jvyduna/BCWW-sign-2018/Physical sign design/CAD/1 HOT/Cuts/Front panel/0.25 layer cuts.pdf

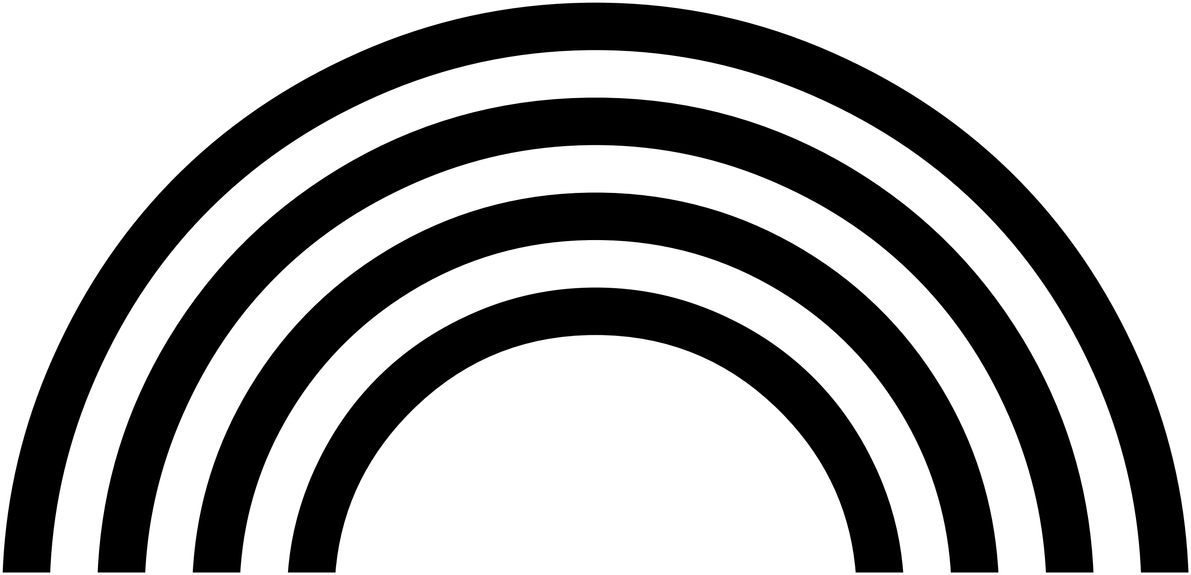
[picture p3: figure]
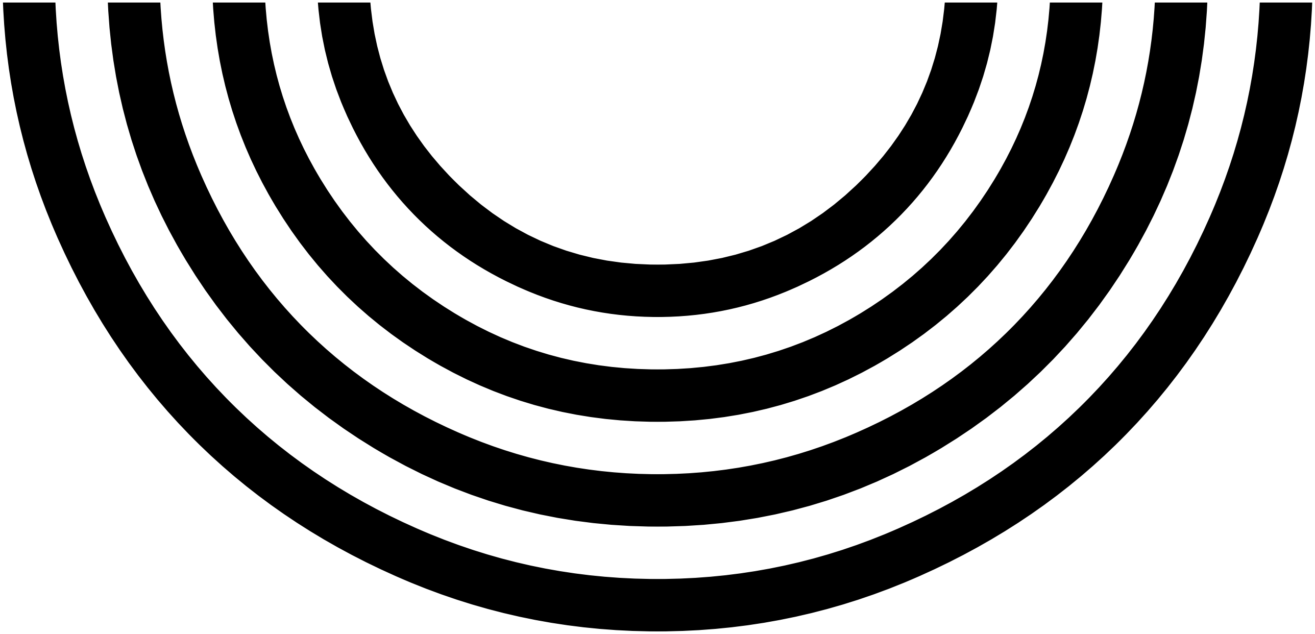
[picture p4: figure]
