jvyduna/BCWW-sign-2018/Physical sign design/CAD/3 CHICKA/Cuts/Border channel/cut path border.pdf

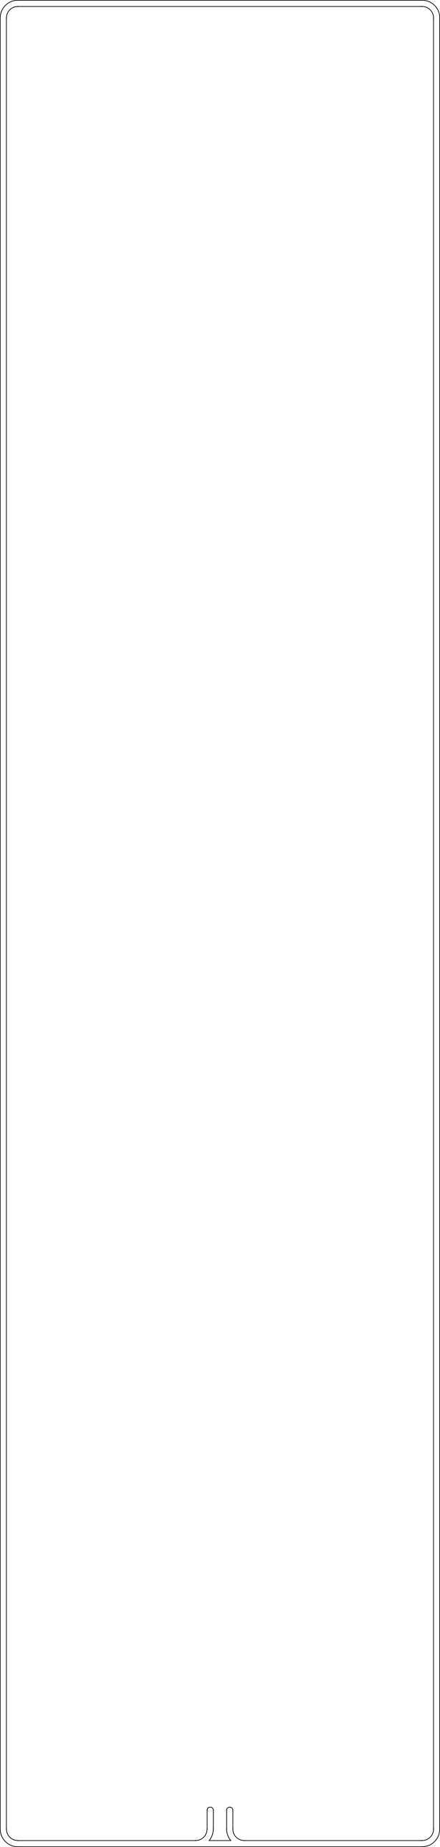
[picture p5: figure]
