jvyduna/BCWW-sign-2018/Physical sign design/2018 Camp placement.png

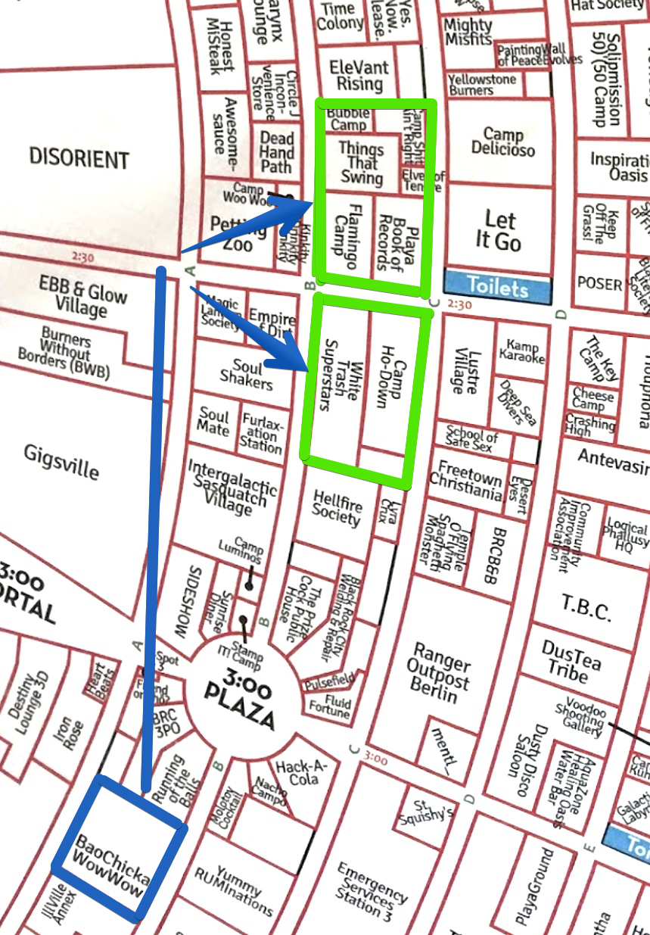
Physical sign design/2018 Camp placement.png
