jvyduna/BCWW-sign-2018/Physical sign design/BCWW signs sunset.jpg

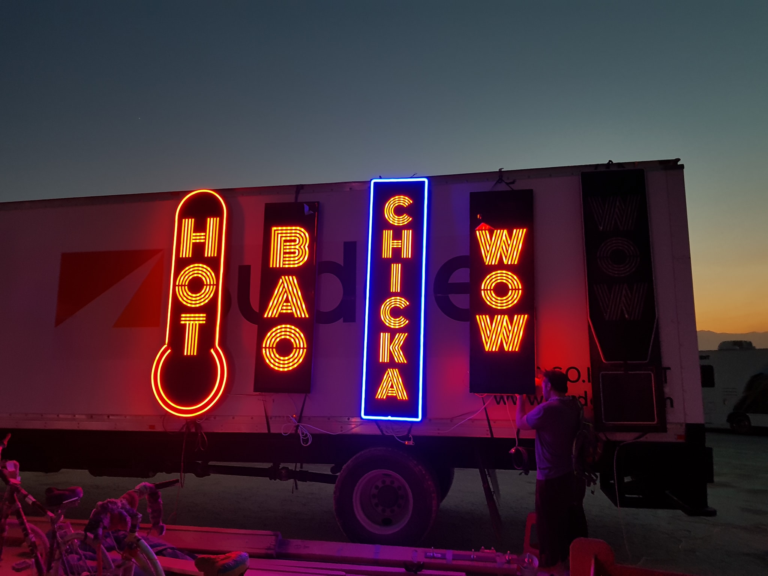
Physical sign design/BCWW signs sunset.jpg
