jvyduna/BCWW-sign-2018/Physical sign design/fonts/mockups/Bauhaus.png

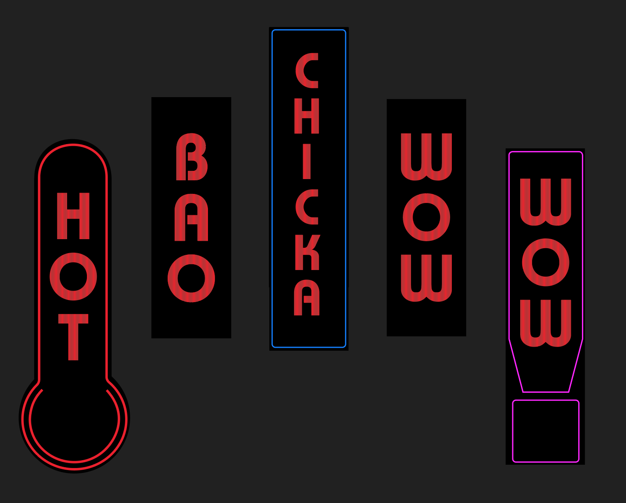
Physical sign design/fonts/mockups/Bauhaus.png
