jvyduna/BCWW-sign-2018/Physical sign design/fonts/mockups/Bungee.png

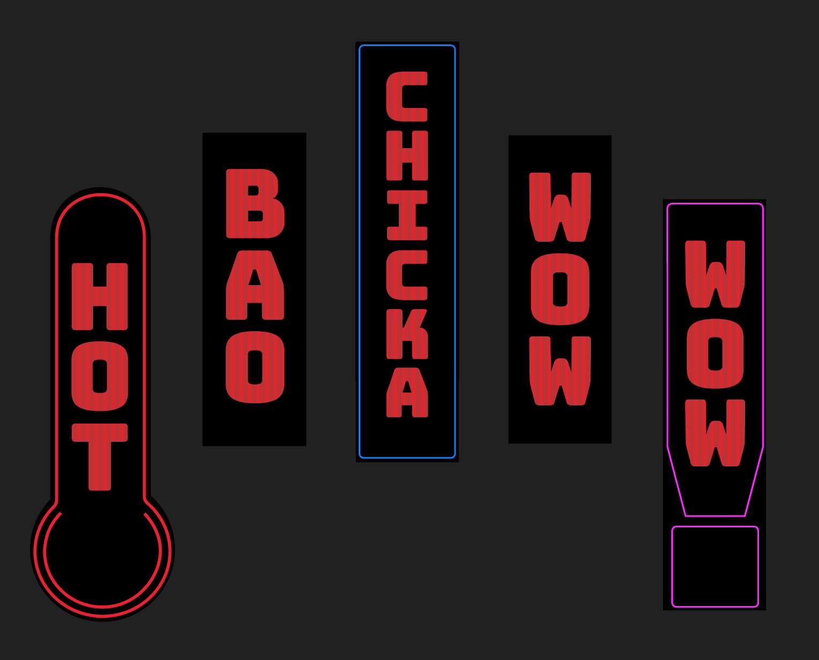
Physical sign design/fonts/mockups/Bungee.png
