jvyduna/BCWW-sign-2018/Physical sign design/fonts/mockups/Delicious.png

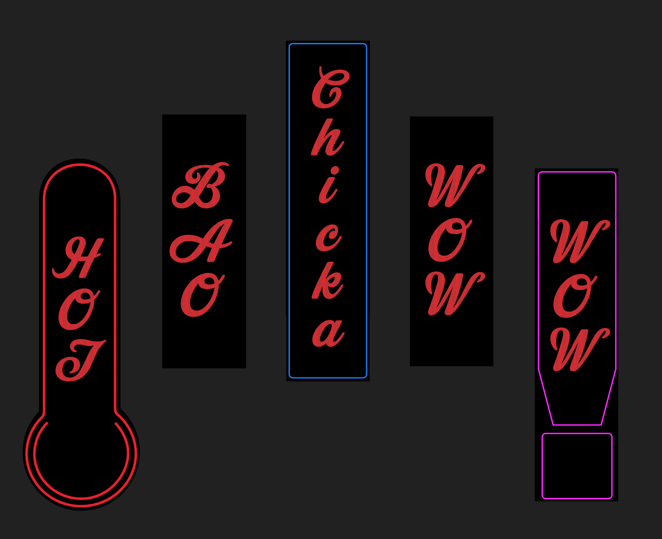
Physical sign design/fonts/mockups/Delicious.png
