jvyduna/BCWW-sign-2018/Physical sign design/fonts/mockups/Idlewild Bold.png

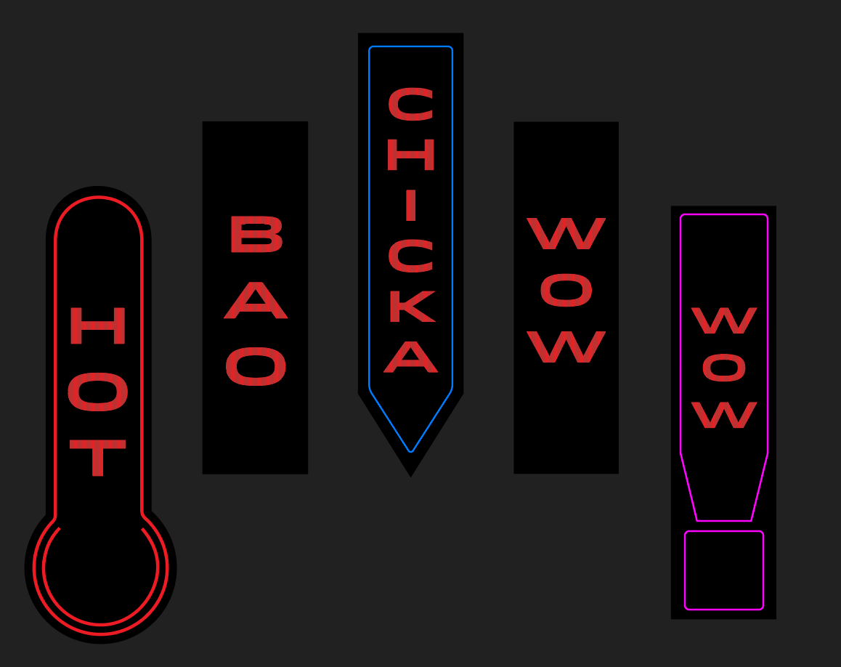
Physical sign design/fonts/mockups/Idlewild Bold.png
