jvyduna/BCWW-sign-2018/Physical sign design/fonts/mockups/Monoton.png

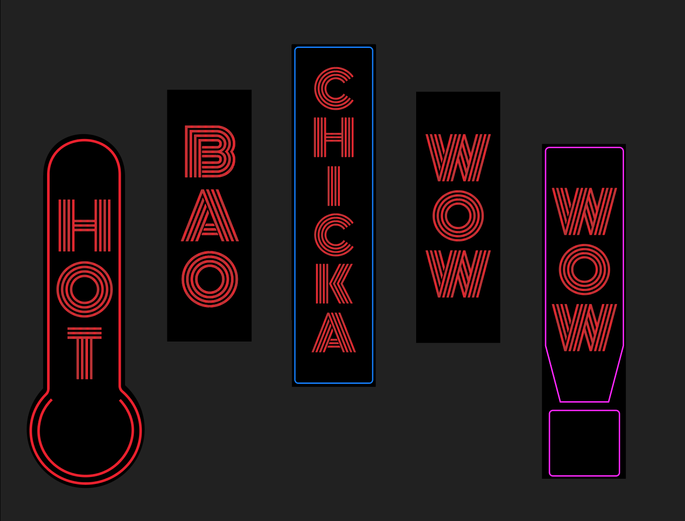
Physical sign design/fonts/mockups/Monoton.png
