jvyduna/BCWW-sign-2018/Physical sign design/fonts/mockups/Ringside.png

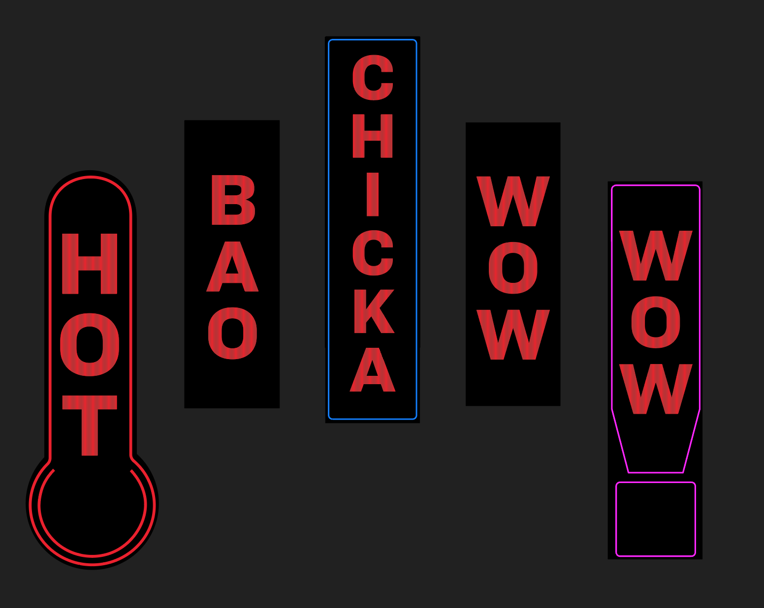
Physical sign design/fonts/mockups/Ringside.png
