jvyduna/BCWW-sign-2018/Physical sign design/Inspiration board/40342030-neon-light-alphabet-font-.jpg

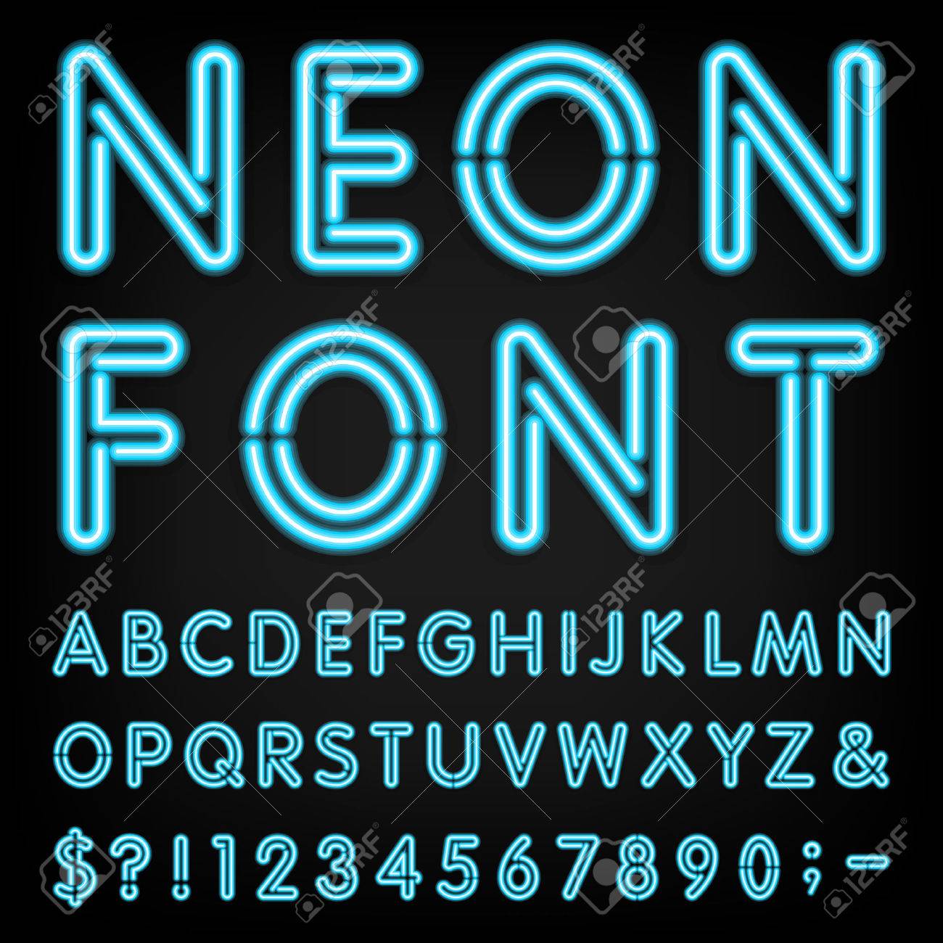
Physical sign design/Inspiration board/40342030-neon-light-alphabet-font-.jpg
