jvyduna/BCWW-sign-2018/Physical sign design/Inspiration board/img.jpg

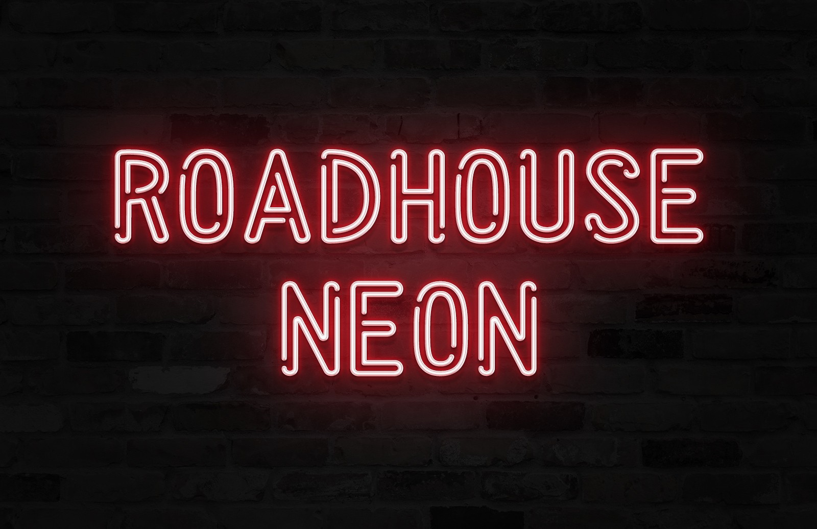
Physical sign design/Inspiration board/img.jpg
