jvyduna/BCWW-sign-2018/Physical sign design/Inspiration board/Neon chinatown.jpg

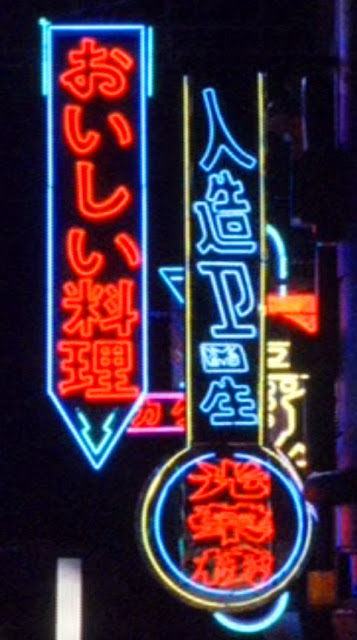
Physical sign design/Inspiration board/Neon chinatown.jpg
