jvyduna/BCWW-sign-2018/Physical sign design/Prototypes/W-N Works.png

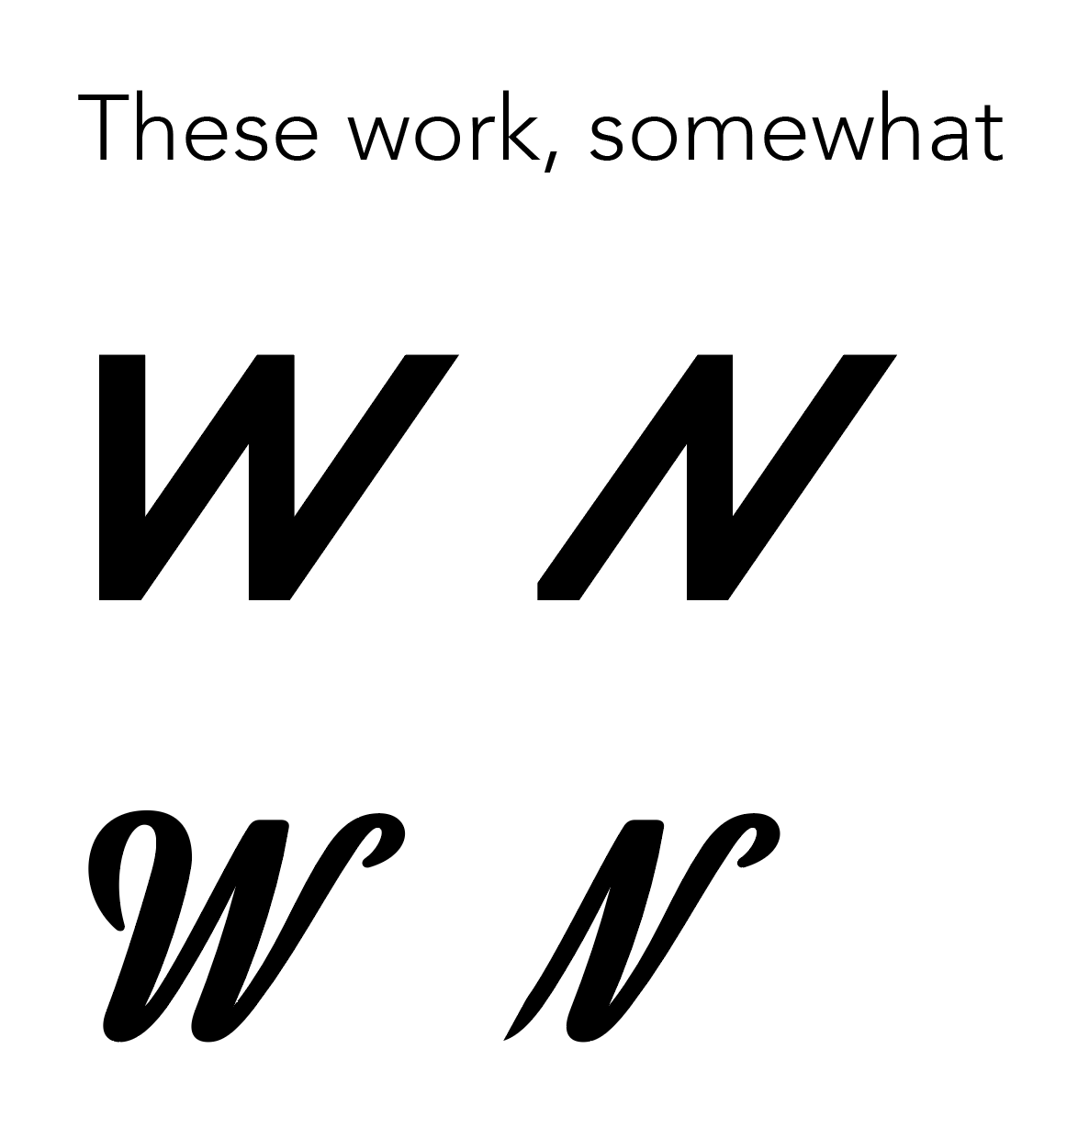
Physical sign design/Prototypes/W-N Works.png
