jvyduna/BCWW-sign-2018/Physical sign design/CAD/5 WOW!/Cuts/CAD Routes - measure 1x3 layer.pdf

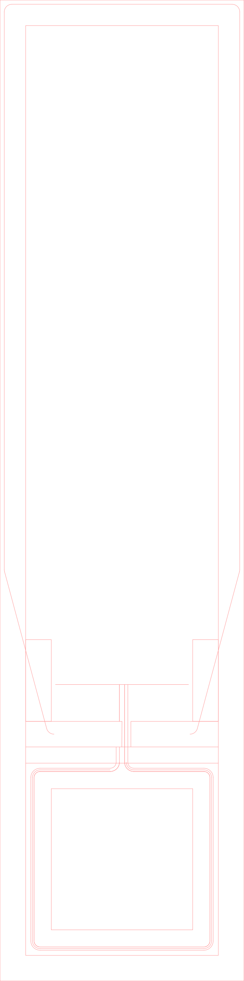
[picture p28: figure]
