jvyduna/BCWW-sign-2018/Physical sign design/CAD/0 BAO test build/Test Core mellow/0.125 font profile exact/Core Mellow exact (1-8" profile).pdf

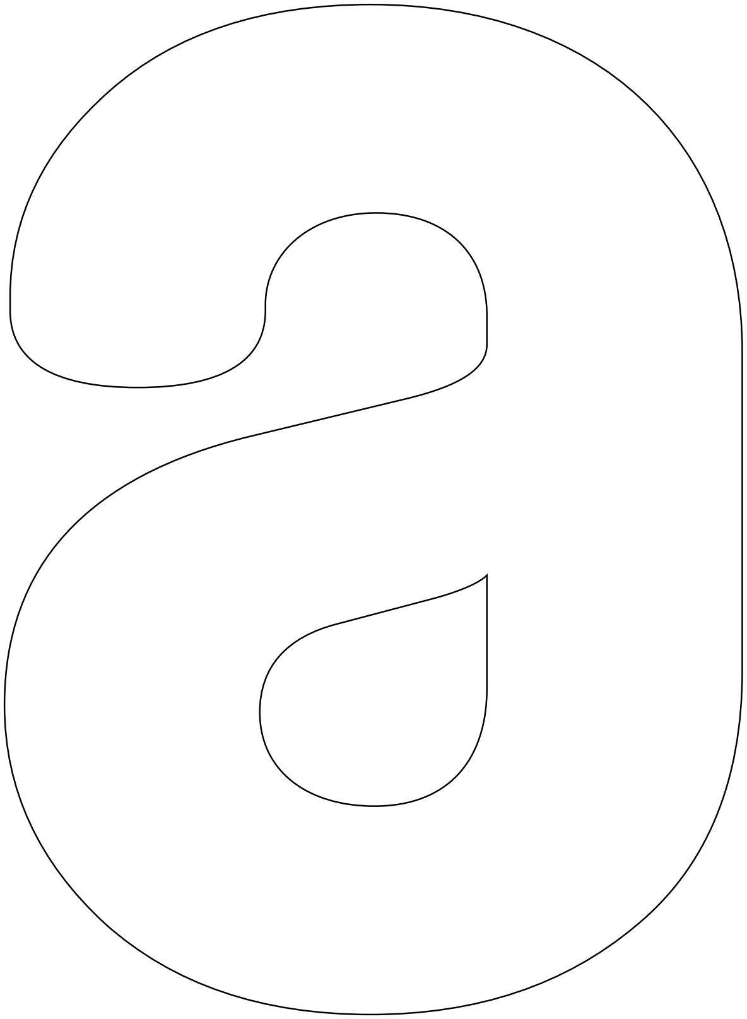
[picture p29: figure]
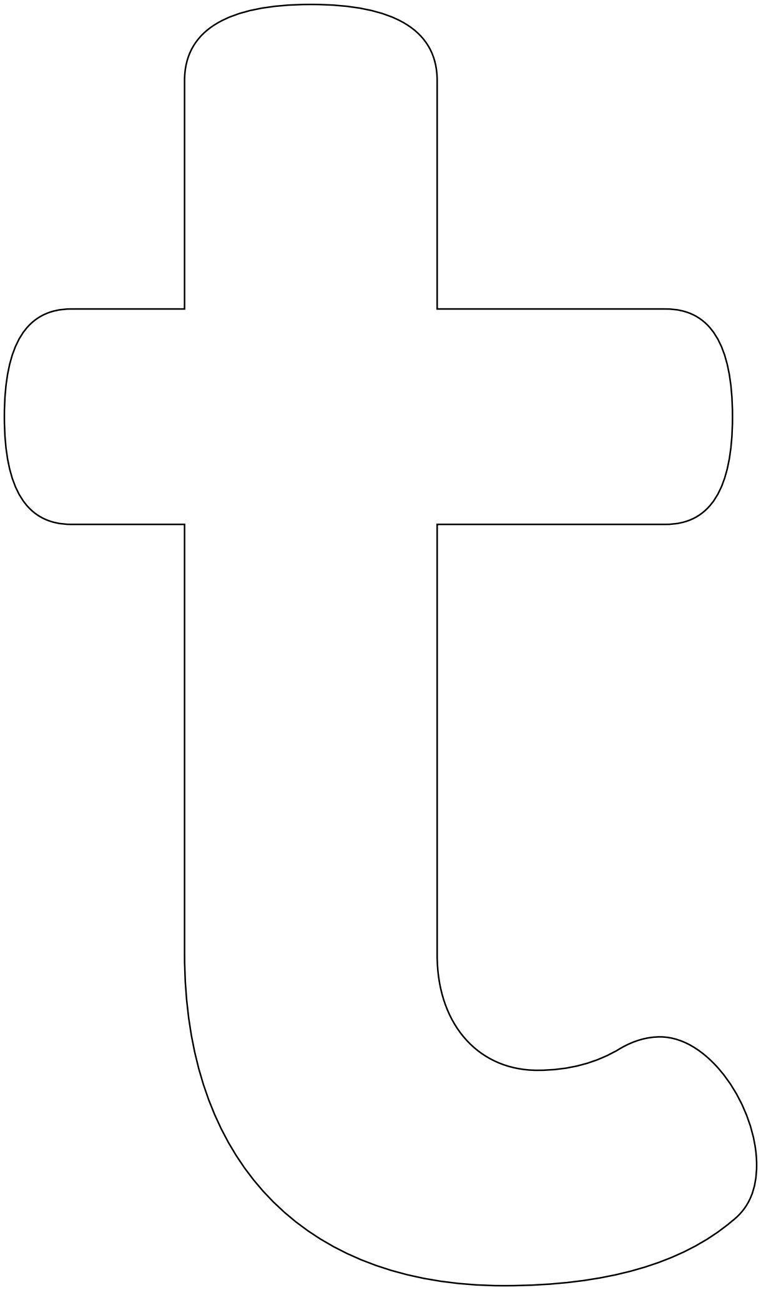
[picture p30: figure]
