jvyduna/BCWW-sign-2018/Physical sign design/CAD/0 BAO test build/Test Core mellow/0.75 pockets rounded/0.75 pocket CM rounded and through.pdf

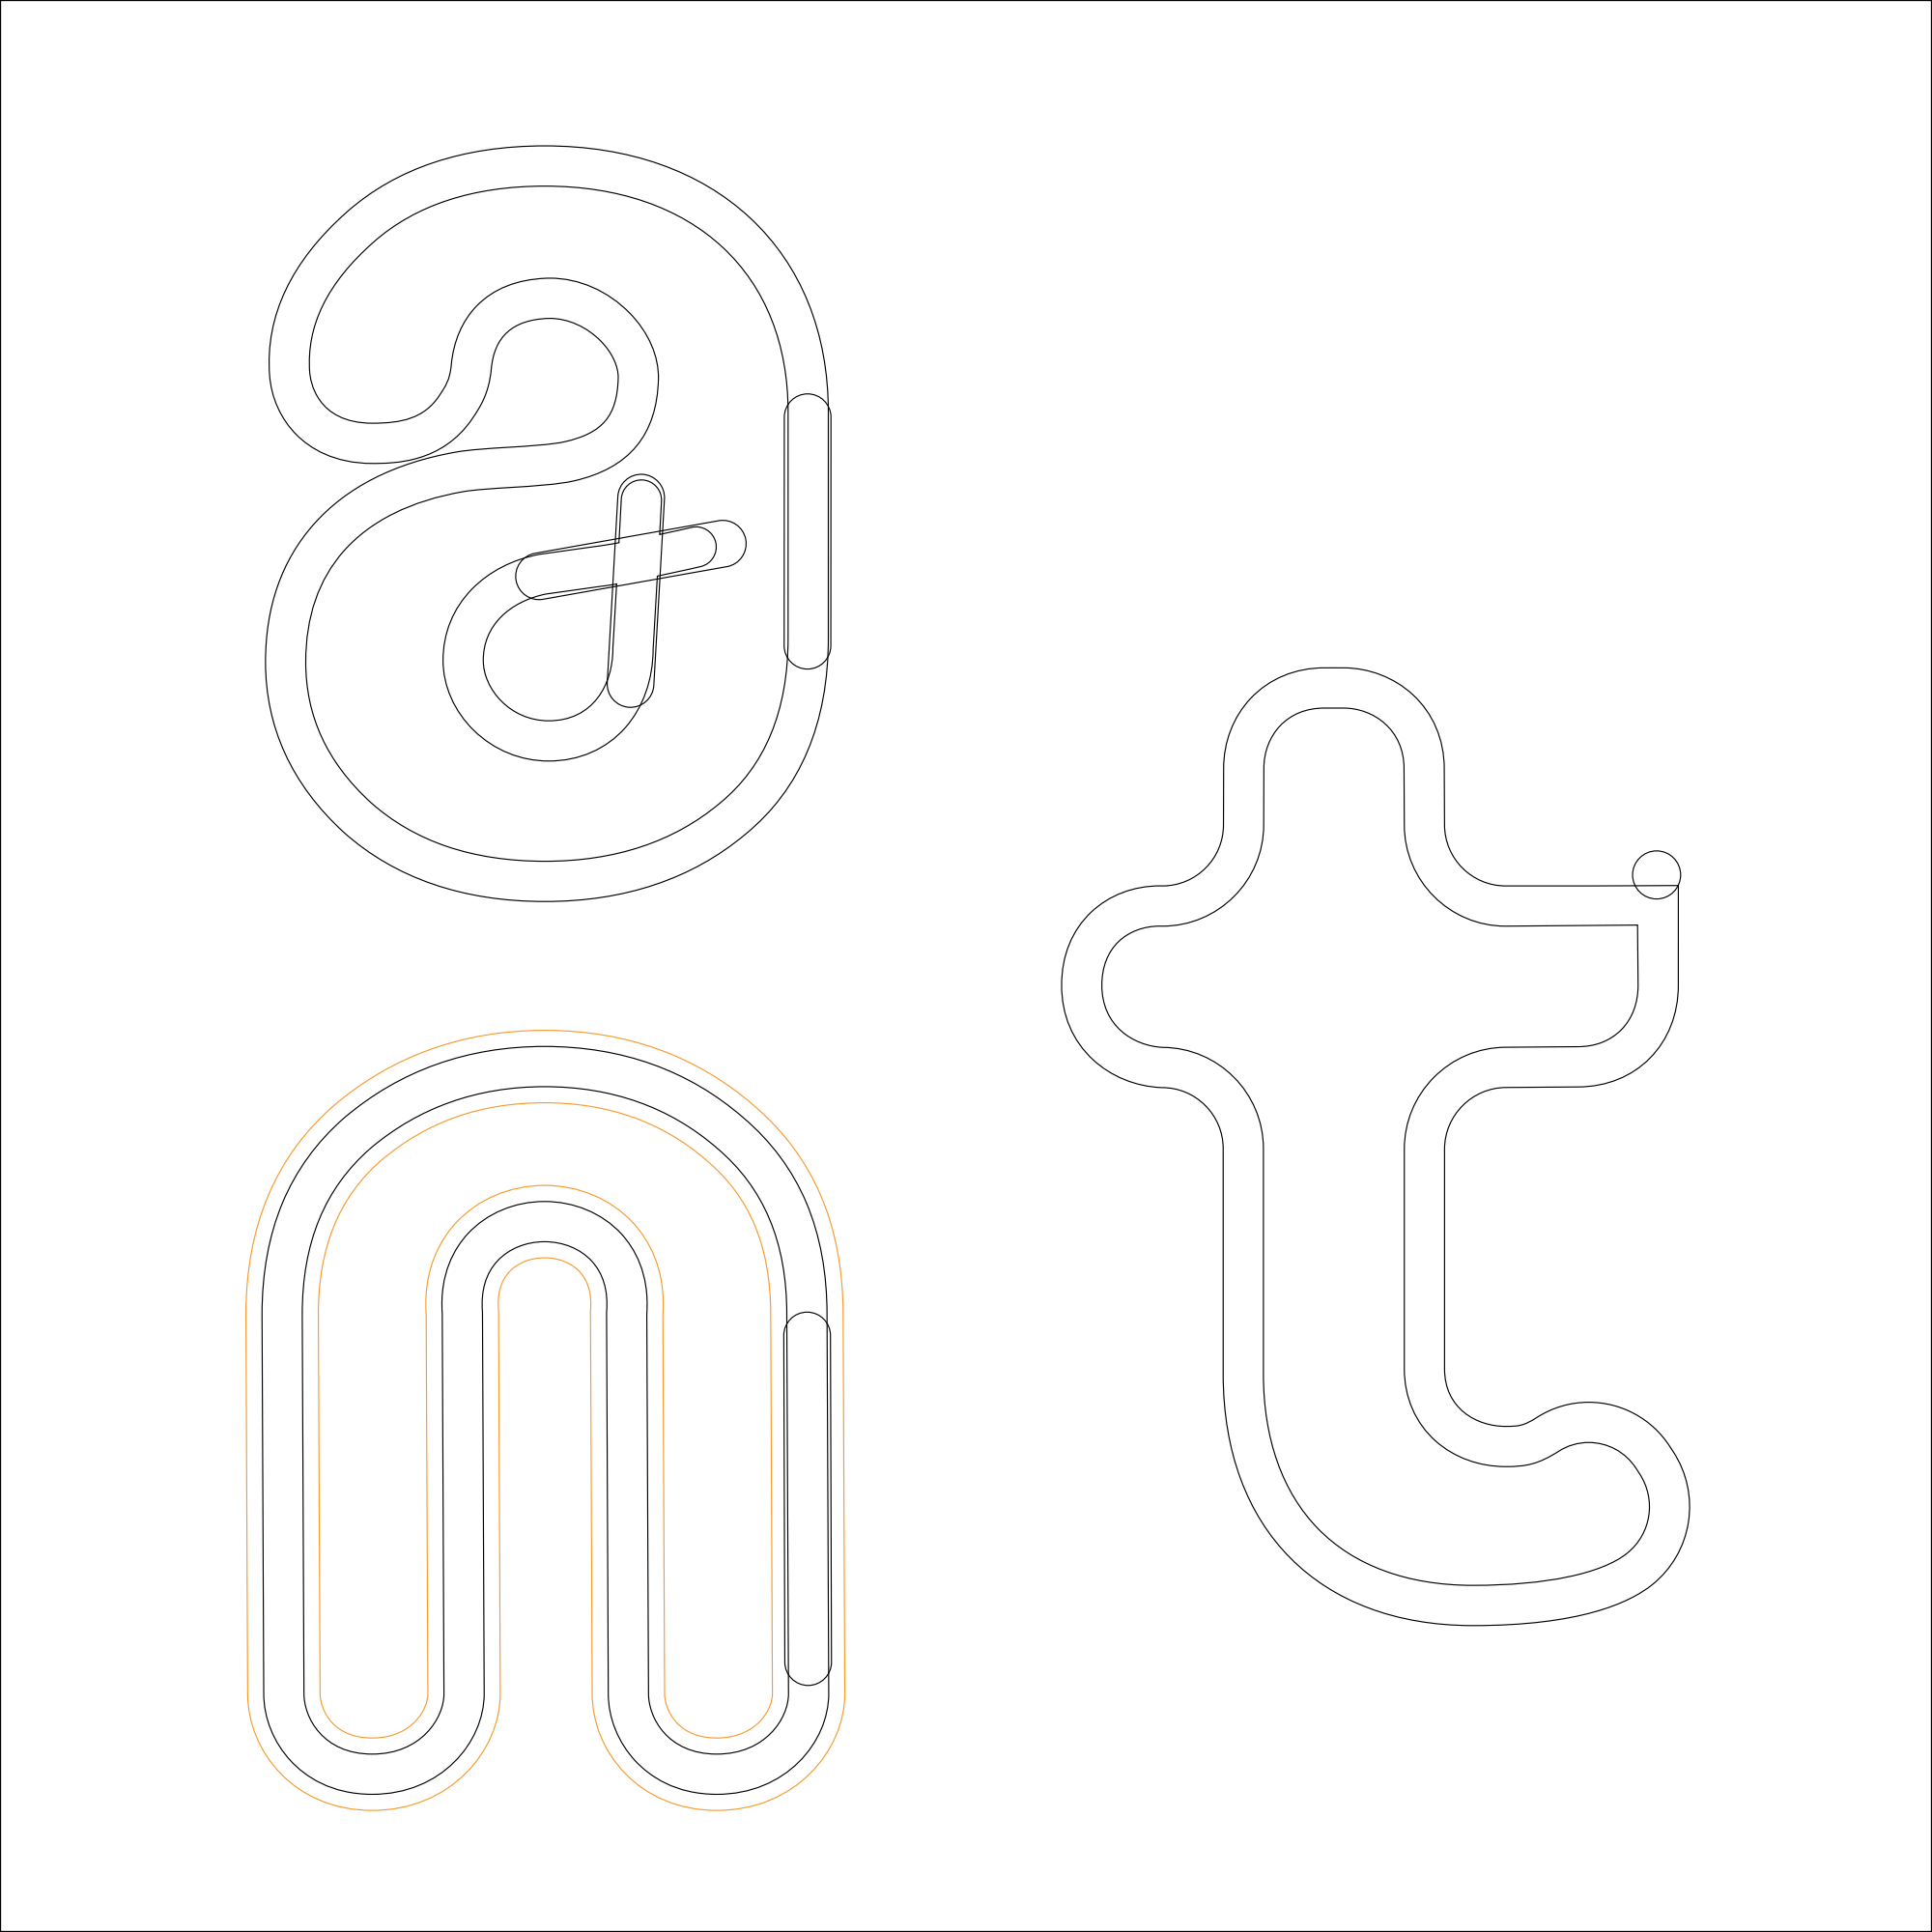
[picture p38: page 1]
