jvyduna/BCWW-sign-2018/Physical sign design/CAD/1 HOT/Cuts/Ply Back/HOT Ply back.pdf

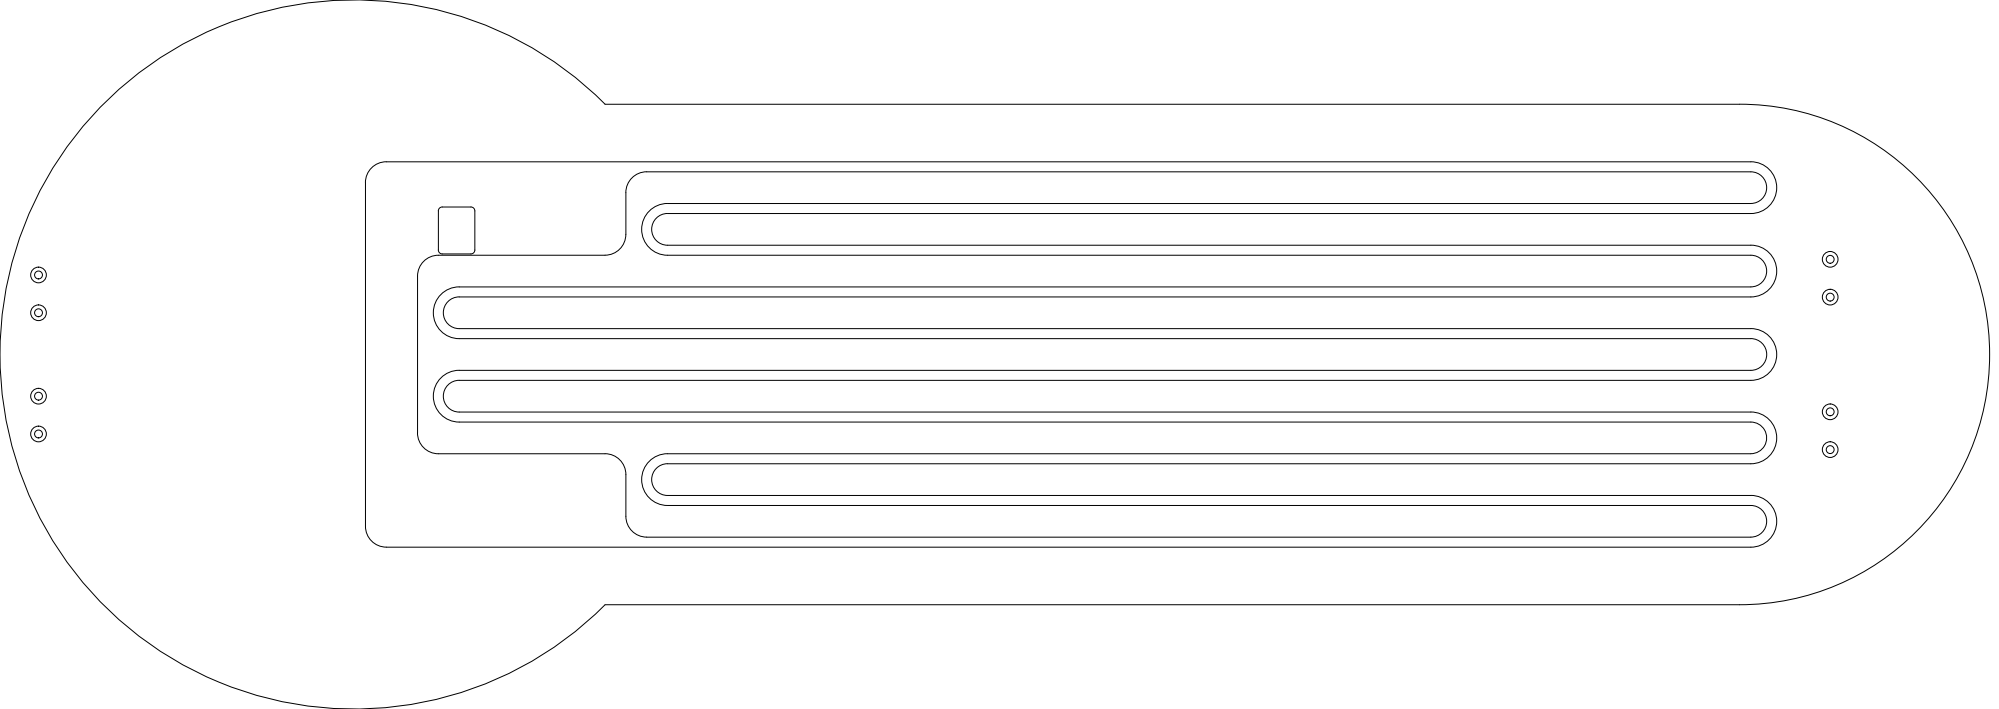
[picture p39: page 1]
