jvyduna/BCWW-sign-2018/Physical sign design/CAD/1 HOT/Cuts/Thermo borders/Thermo borders.pdf

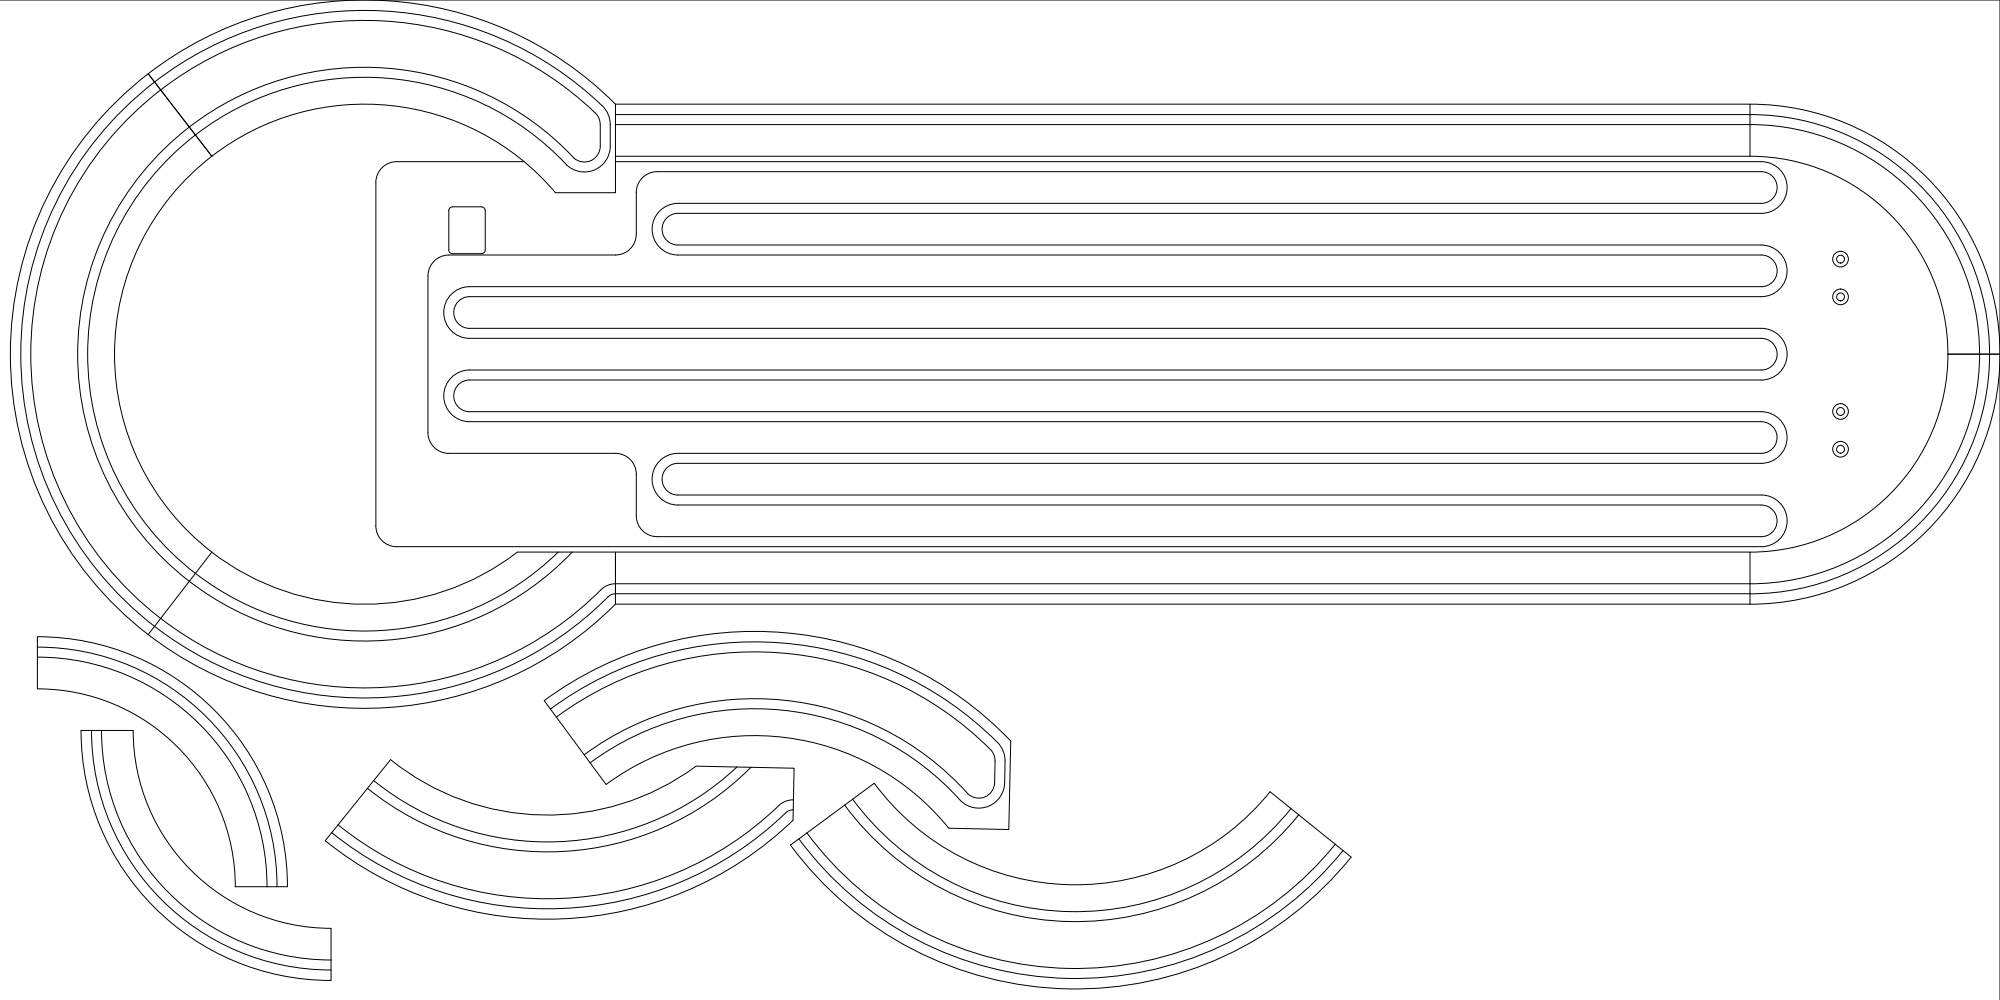
[picture p40: page 1]
