jvyduna/BCWW-sign-2018/Physical sign design/CAD/3 CHICKA/Cuts/Front panel/Front panel cuts.pdf

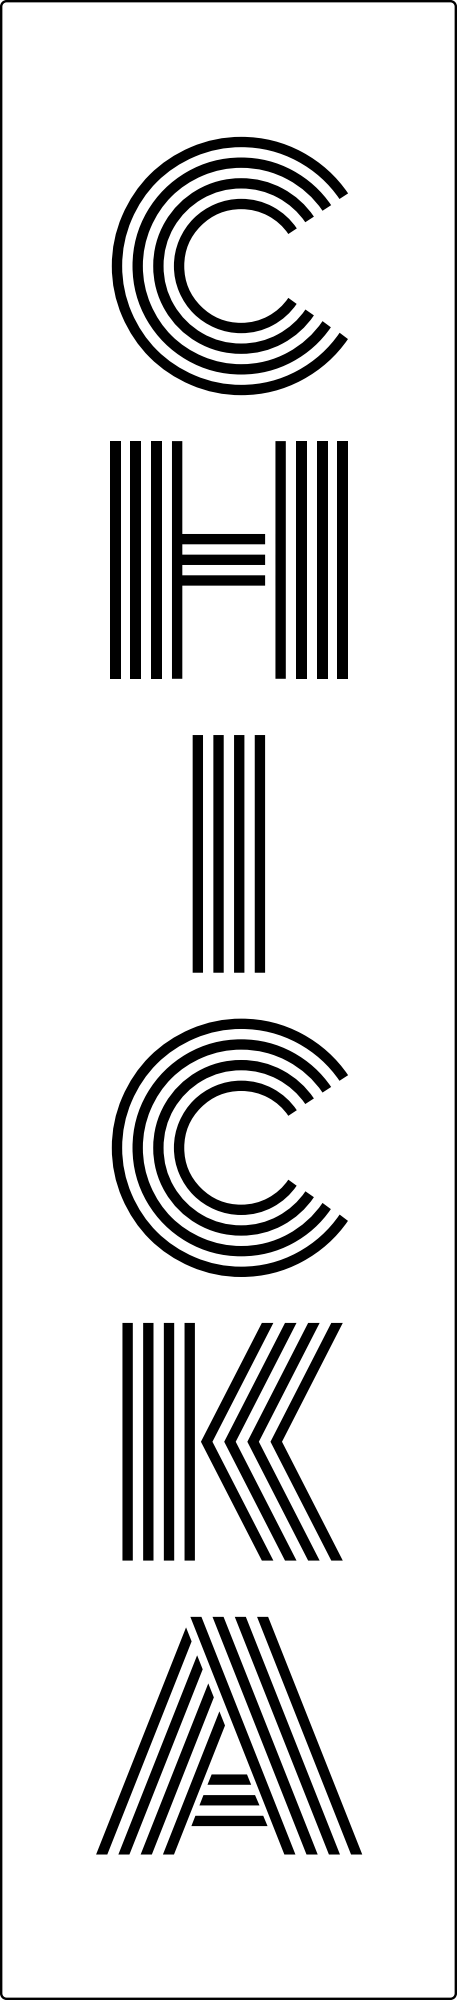
[picture p41: page 1]
