jvyduna/BCWW-sign-2018/Physical sign design/CAD/3 CHICKA/Cuts/Ply back/CHICKA Ply back.pdf

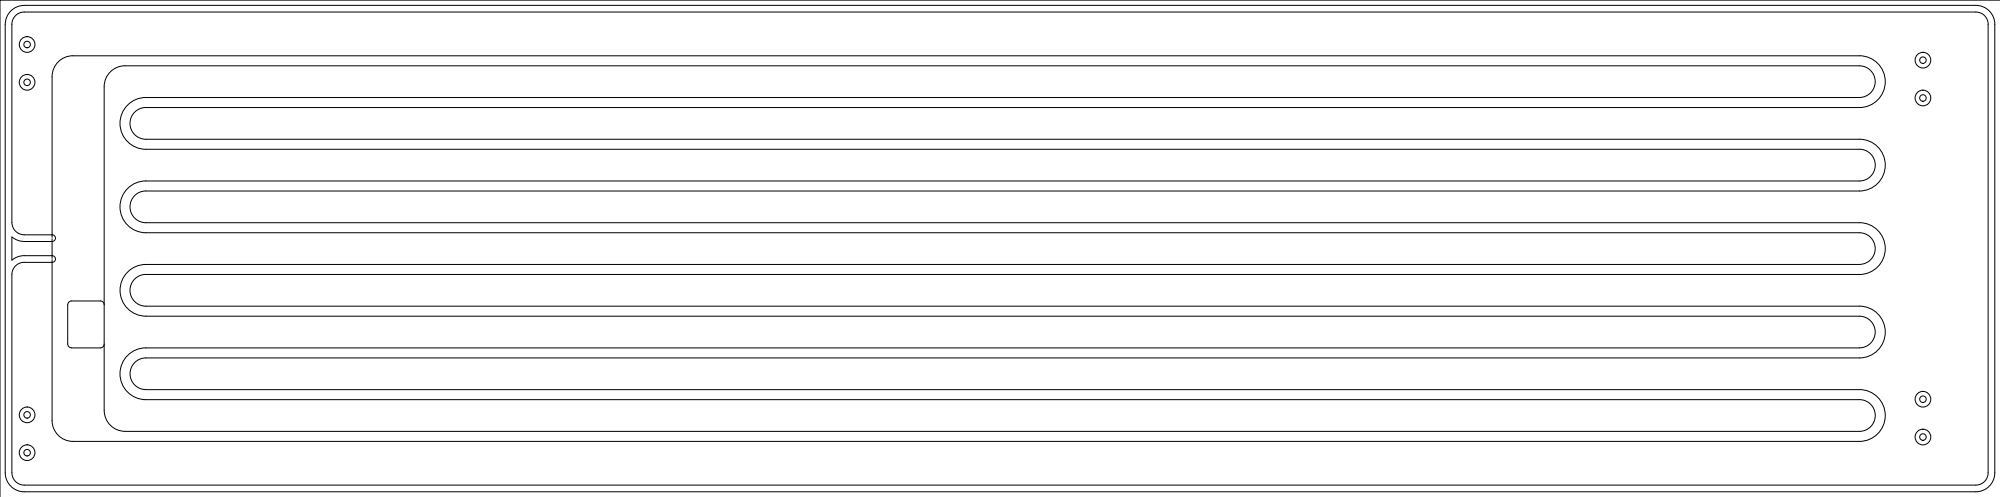
[picture p42: page 1]
