jvyduna/BCWW-sign-2018/Physical sign design/CAD/4 NWOW/Cuts/Front panel/0.25 ply front NWOW.pdf

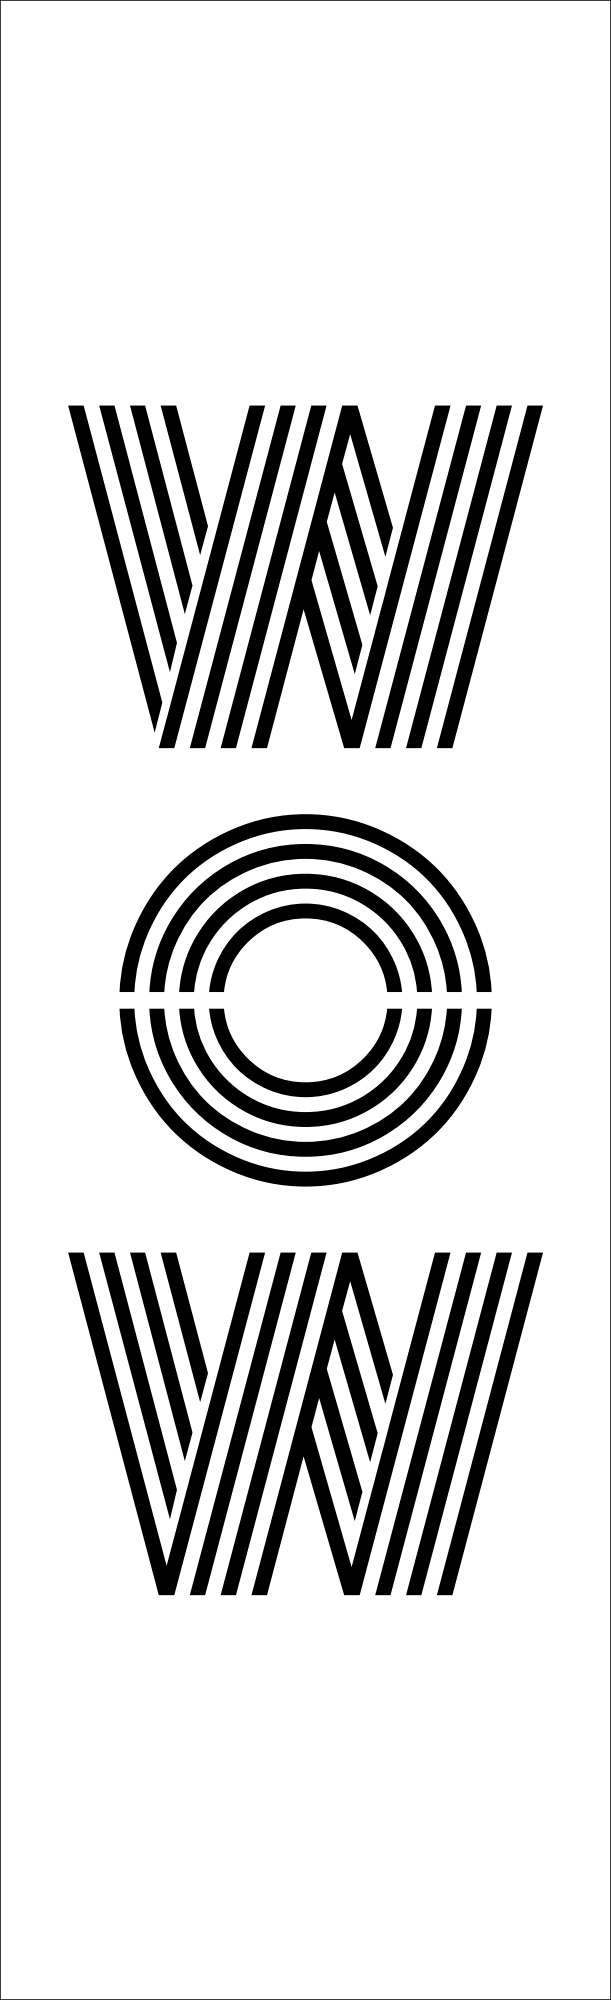
[picture p43: page 1]
