jvyduna/BCWW-sign-2018/Physical sign design/CAD/5 WOW!/Cuts/Front panel/Front panel cuts.pdf

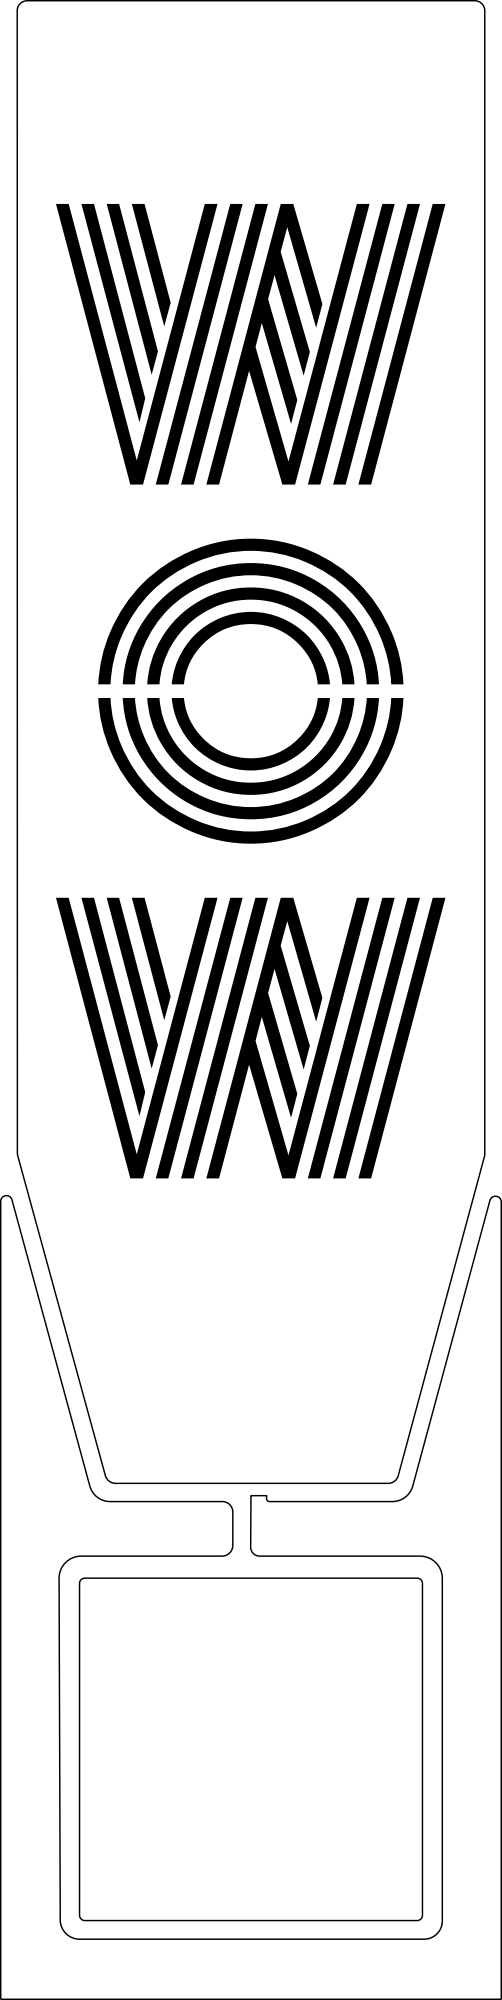
[picture p44: page 1]
